bartkepl/SFP-xSPI_Bridge/doc/vhdl/8b10b.md

# Kod 8b/10b: `code8b10b_pkg`, `enc_8b10b`, `dec_8b10b`

Pliki: `vhdl/sfp_bridge/src/pkg/code8b10b_pkg.vhd`, `src/link/enc_8b10b.vhd`, `src/link/dec_8b10b.vhd` · testbench: `vhdl/sim/tb/tb_8b10b.vhd`

Kod liniowy łącza ([plan, rozdz. 7.2](../sfp-xspi-bridge-plan.md)): 8b/10b Widmera–Franaszka w postaci z IEEE 802.3 (rozdz. 36) i Fibre Channel. Zapewnia składową stałą równą zeru (sprzężenie AC w module SFP), maksymalnie 5 jednakowych bitów z rzędu (odzysk zegara) oraz znaki sterujące, w tym comma do wyrównania słów.

## Konwencja bitów

| Element | Zapis |
|---|---|
| bajt | `data(7 downto 0)` = H G F E D C B A; znak Dx.y: x = EDCBA (0–31), y = HGF (0–7) |
| symbol | `code(9 downto 0)`, `code(0)` = a, `code(1)` = b, …, `code(5)` = i, `code(6)` = f, …, `code(9)` = j |
| kolejność nadawania | `code(0)` (bit a) jako pierwszy |
| dysparytet bieżący (RD) | `'0'` = RD−, `'1'` = RD+ |

Znaki sterujące (z `k = '1'`): K28.0–K28.7, K23.7, K27.7, K29.7, K30.7. Sekwencja comma `0011111` / `1100000` (bity a…f) występuje tylko w K28.1, K28.5 i K28.7. W protokole łącza: K28.5 + D16.2 — bezczynność, K27.7 — początek ramki, K29.7 — koniec ramki ([plan, `tx_framer`](../sfp-xspi-bridge-plan.md)); stałe w `bridge_pkg`.

## Jedno źródło definicji

Tablice 5b/6b i 3b/4b oraz reguły dysparytetu i zamiany D.x.P7 → D.x.A7 są zapisane raz, w funkcji `encode_8b10b` pakietu `code8b10b_pkg`. Tablica dekodera (1024 pozycje) jest wyliczana z tej funkcji w czasie elaboracji (`build_dec_table`), więc koder i dekoder nie mogą się rozejść. Niezależną kontrolę samej funkcji zapewnia testbench (wzorce ze standardu i własności kodu).

## `enc_8b10b`

| Port | Kierunek | Opis |
|---|---|---|
| `clk`, `rst` | in | zegar, reset synchroniczny (RD ← RD−) |
| `en` | in | nowy bajt |
| `data[7:0]`, `k` | in | znak do zakodowania |
| `code[9:0]` | out | symbol (`code(0)` nadawany pierwszy) |
| `valid` | out | nowy symbol na `code` (impuls 1 takt) |
| `k_err` | out | zażądano nieprawidłowego znaku sterującego; zakodowano znak danych o tej wartości |
| `rd` | out | dysparytet po symbolu |

**Opóźnienie:** 1 takt. Między impulsami `en` wyjście `code` trzyma ostatni symbol (serializer pobiera symbol co 10 okresów bitu).

## `dec_8b10b`

| Port | Kierunek | Opis |
|---|---|---|
| `clk`, `rst` | in | zegar, reset synchroniczny (oczekiwany RD ← RD−) |
| `en`, `code[9:0]` | in | wyrównany symbol |
| `data[7:0]`, `k` | out | znak (ważny, gdy `code_err = '0'`) |
| `valid` | out | wynik ważny (impuls 1 takt) |
| `code_err` | out | słowo spoza kodu (w żadnym dysparytecie) |
| `disp_err` | out | słowo poprawne, ale nie dla bieżącego dysparytetu |
| `rd` | out | dysparytet po symbolu |

**Potok:**

1. odczyt tablicy (1024 × 13 bitów: znak, `k`, poprawność dla RD− i RD+, waga 4/6) — synteza umieszcza ją w jednym bloku BSRAM jako ROM;
2. kontrola poprawności i dysparytetu, aktualizacja RD z wagi symbolu (6 jedynek → RD+, 4 → RD−, 5 → bez zmian).

**Opóźnienie:** 2 takty. Po błędzie dysparytetu dekoder przyjmuje dysparytet wynikający z odebranego symbolu, więc pojedynczy błąd nie wywołuje serii kolejnych.

Waga symbolu jest zapisana w tablicy zamiast liczenia jedynek w logice — w wersji z liczeniem ścieżka sprzężenia zwrotnego RD miała 9,2 ns.

## Testbench `tb_8b10b`

| Część | Sprawdzenie |
|---|---|
| A | 22 znaki wzorcowe w obu dysparytetach, zapisane jako `"abcdei fghj"` z tabel standardu: D0.0, D21.5, D10.2, D16.2, D7.0, D3.3, D17.7, D11.7, D31.7, D23.7, D20.7, D18.7, D13.7, D14.7, K28.5, K28.1, K28.7, K28.0, K23.7, K27.7, K29.7, K30.7 |
| B | wszystkie 268 znaków × 2 dysparytety: waga symbolu 4/5/6 i bloków, RD− nigdy nie daje wagi 4, RD+ nigdy 6, poprawne RD po symbolu, jednoznaczność symboli, comma tylko w K28.1/5/7, seria 5 jednakowych bitów wewnątrz symbolu tylko w K28.1/5/7 (pozostałe ≤ 4) |
| C | 20 000 losowych znaków (dane, K28.5 i inne sterujące) przez koder i dekoder: brak błędów, zgodność znaków, seria ≤ 5 w strumieniu, bieżąca suma cyfrowa w zakresie −3…+3, comma wyłącznie na granicy symbolu |
| D | wstrzyknięcie błędów: `0000000000` → `code_err`; K28.5 w postaci RD+ przy oczekiwanym RD− → `disp_err`, znak nadal rozpoznany jako K28.5 |

Test mutacyjny wykazał lukę w pierwszej wersji testbencha (pominięcie D20 w regule A7 nie było wykrywane); dodano wzorce D.x.7 oraz kontrolę serii wewnątrz symbolu. Obecnie wykrywane są: błąd reguły A7, błąd pozycji tablicy 5b/6b, brak flagi dysparytetu.

## Przebieg

`.\view.ps1 tb_8b10b` — czas symulacji ok. 200 µs (20 000 znaków po 10 ns).

- **Początek (ok. 20–200 ns):** po zwolnieniu `rst` koder dostaje znak w każdym takcie. `enc_code` zmienia się takt po `enc_data`; `enc_rd` przełącza się tylko po symbolach niezrównoważonych.
- **Dekoder:** `dec_data` i `dec_k` powtarzają `enc_data` i `enc_k` z opóźnieniem 3 taktów (1 koder + 2 dekoder); `u_dec.en_q` pokazuje pierwszy stopień potoku. `dec_cerr` i `dec_derr` pozostają `0` przez cały strumień.
- **K28.5 na przebiegu:** `enc_data = BC` przy `enc_k = 1`; w formacie binarnym `enc_code` = `0101111100` (RD−) lub `1010000011` (RD+) — zapis od `code(9)` do `code(0)`, czyli odwrotnie do kolejności nadawania.
- **Koniec (ok. 200,0–200,1 µs):** wstrzyknięte symbole — `dec_cerr = 1` po `0000000000`, następnie `dec_derr = 1` przy K28.5 o złym dysparytecie (`dec_k = 1`, `dec_data = BC`).
