bartkepl/SFP-xSPI_Bridge/vhdl/sim/tb/tb_link_frames.vhd

--------------------------------------------------------------------------------
-- tb_link_frames
--
-- Testbench for tx_framer and rx_deframer: full-duplex link at character
-- level (no serializer / CDR), with real FIFOs and 8b/10b coding:
--
--   side A: TX FIFO -> tx_framer -> enc_8b10b --(channel A->B)--> side B
--   side B: dec_8b10b -> rx_deframer -> RX FIFO (8 KiB) -> reader
--   reverse direction carries B's idle pairs (XON/XOFF) back to side A.
--
-- One character per 5 clock cycles (100 Mbaud at clk_sys = 50 MHz, ADR 0007).
--
-- Model: payload, type and length of frame <id> are pure functions of id;
-- ids of frames that must arrive are queued, the reader compares every
-- received frame with the head of the queue.
--
-- Phases and checks:
--   1. 20 frames, length 1..300: all delivered intact and in order.
--   2. 6 frames with one bit flipped in one symbol of the frame: each is
--      dropped with exactly one error event (code/disparity, CRC, length or
--      framing); the frames around them are delivered.
--   2b. 3 frames with a wrong byte carried by a valid symbol (payload, CRC0,
--      TYPE): each dropped with ev_crc_err.
--   3. LEN = 0 and LEN = 1025 written by the host: both rejected with
--      ev_len_err (framer flags len_err for 1025); the next frame delivered.
--   4. Character sync lost on side B in the middle of a frame: the frame is
--      dropped, later frames delivered.
--   4b. Side B receiver not ready (idle /R/, ADR 0008): side A sees
--      remote_ready = '0' and XOFF and does not start a frame for 2000
--      cycles; after B becomes ready the frame is delivered.
--   5. Flow control: reader on side B stopped while 16 frames of 1000 bytes
--      are sent (twice the RX FIFO size). Side B must send XOFF, side A must
--      pause for at least 10000 cycles; no overflow (ev_ovf = 0); after the reader resumes all frames
--      are delivered and XOFF is released.
--   6. Final: every expected frame received, event counters as expected,
--      no frame delivered twice or out of order.
--
-- Waveform: char stream A (char_en, a_cd, a_ck), channel symbols, B deframer
-- state and events, B RX FIFO level, XOFF signals; see doc/vhdl/framing.md.
--------------------------------------------------------------------------------

library ieee;
use ieee.std_logic_1164.all;
use ieee.numeric_std.all;
use ieee.math_real.all;

library work;
use work.tb_pkg.all;
use work.bridge_pkg.all;
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
